lstranskyTGM/uWeatherNG/Hardware/Anemometer/Anemometer_Top.stl

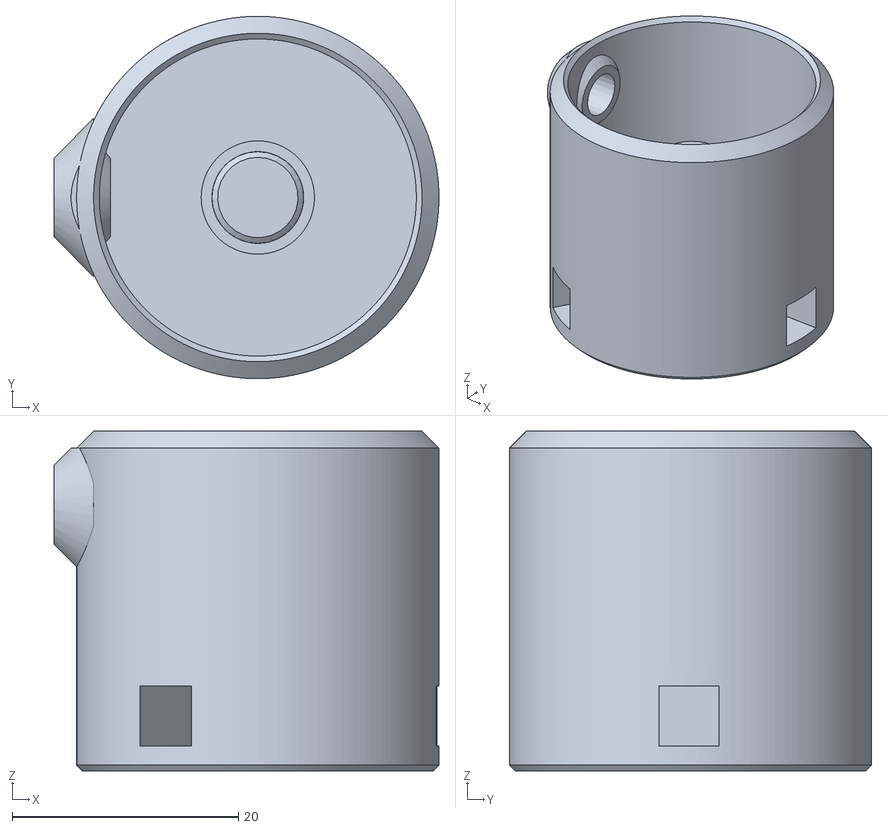
[picture p25: CAD file, 2024-08-01]
Hardware/Anemometer/Anemometer_Top.stl
34.0 x 32.0 x 30.0
