lstranskyTGM/uWeatherNG/Hardware/Connectors/Plug_Joint_ExternalThread.stl

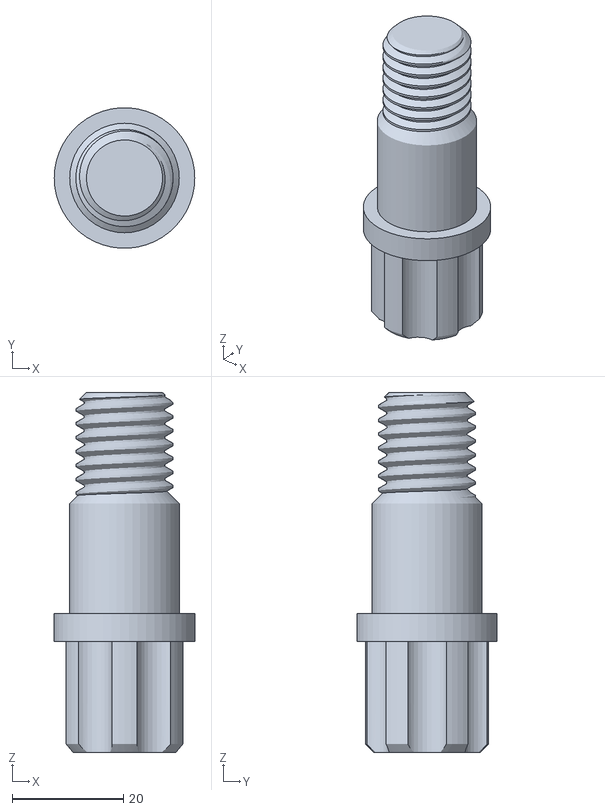
[picture p26: CAD file, 2024-08-01]
Hardware/Connectors/Plug_Joint_ExternalThread.stl
25.3 x 25.3 x 64.8
