lstranskyTGM/uWeatherNG/Hardware/Vane/Vane_Fin.stl

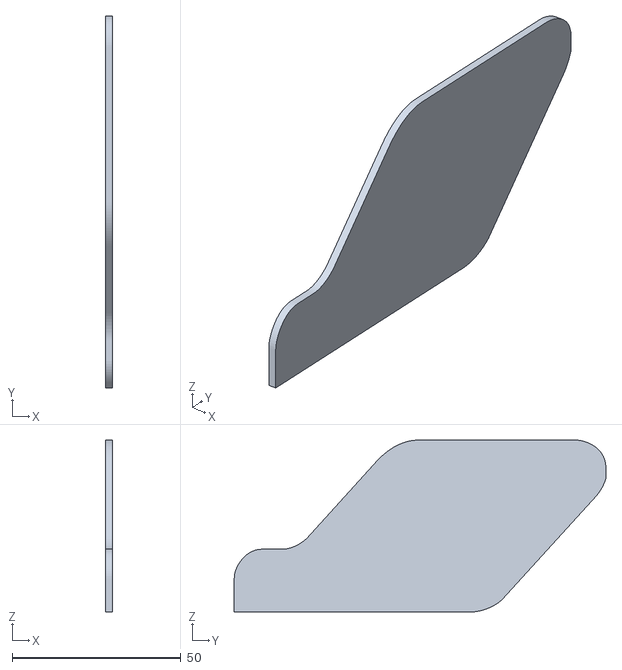
[picture p27: CAD file, 2024-08-01]
Hardware/Vane/Vane_Fin.stl
2.00 x 110.2 x 51.0
