lstranskyTGM/uWeatherNG/Hardware/Anemometer/Anemometer_Body.stl

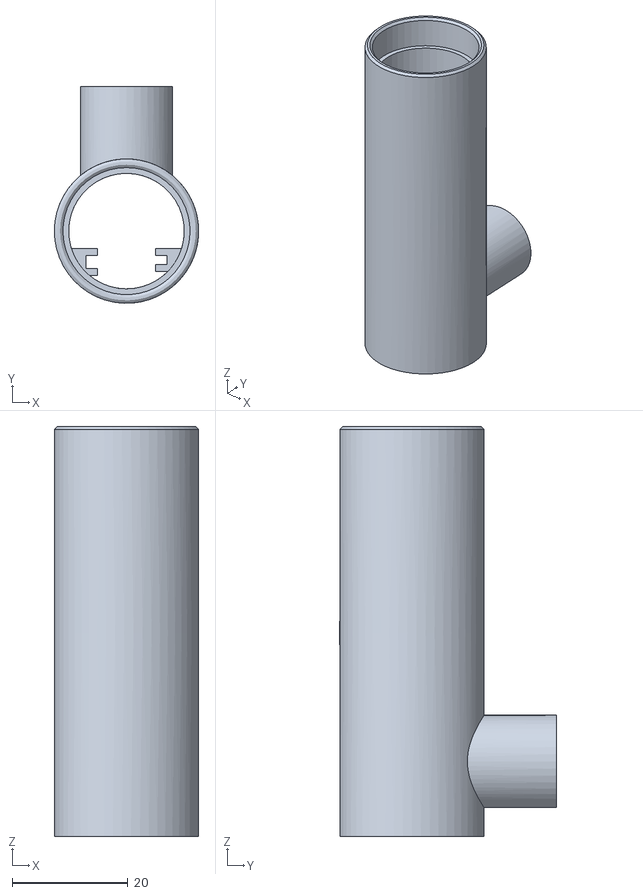
[picture p28: CAD file, 2024-08-01]
Hardware/Anemometer/Anemometer_Body.stl
25.0 x 37.5 x 71.0
