lstranskyTGM/uWeatherNG/Hardware/Connectors/Joint_InternalThread_ExternalThread.stl

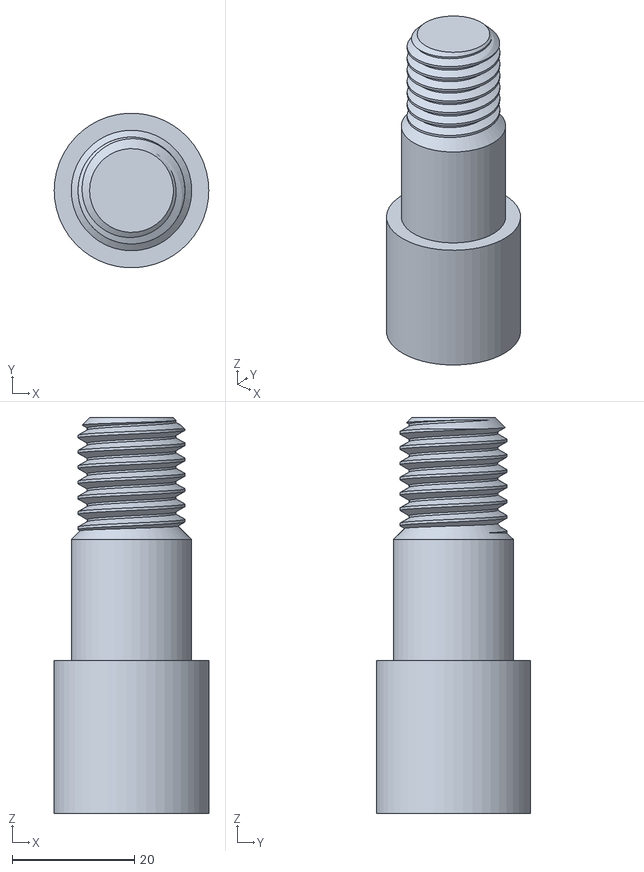
[picture p29: CAD file, 2024-08-01]
Hardware/Connectors/Joint_InternalThread_ExternalThread.stl
25.3 x 25.3 x 64.8
