lstranskyTGM/uWeatherNG/Hardware/Vane/Vane_Fin_Mount.stl

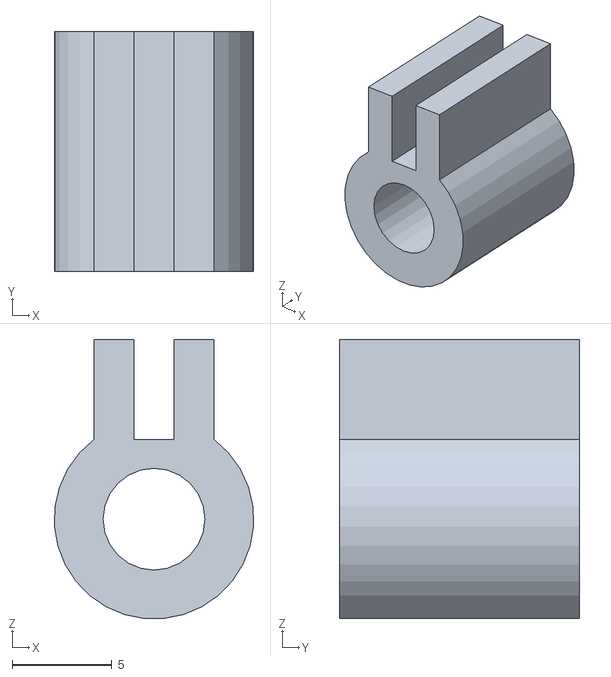
[picture p30: CAD file, 2024-08-01]
Hardware/Vane/Vane_Fin_Mount.stl
9.97 x 12.0 x 14.0
