lstranskyTGM/uWeatherNG/Hardware/Connectors/Plug_Spike.stl

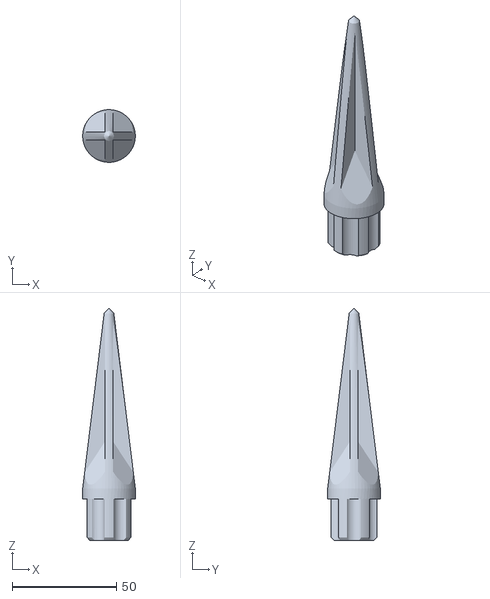
[picture p31: CAD file, 2024-08-01]
Hardware/Connectors/Plug_Spike.stl
25.3 x 25.3 x 111.4
