lstranskyTGM/uWeatherNG/Hardware/Vane/Vane_Top.stl

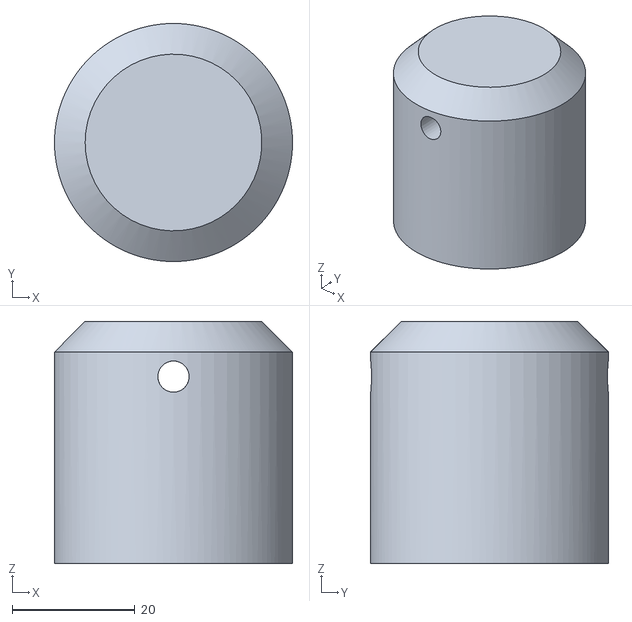
[picture p32: CAD file, 2024-08-01]
Hardware/Vane/Vane_Top.stl
38.8 x 38.8 x 39.5
