lstranskyTGM/uWeatherNG/Hardware/Connectors/Joint.stl

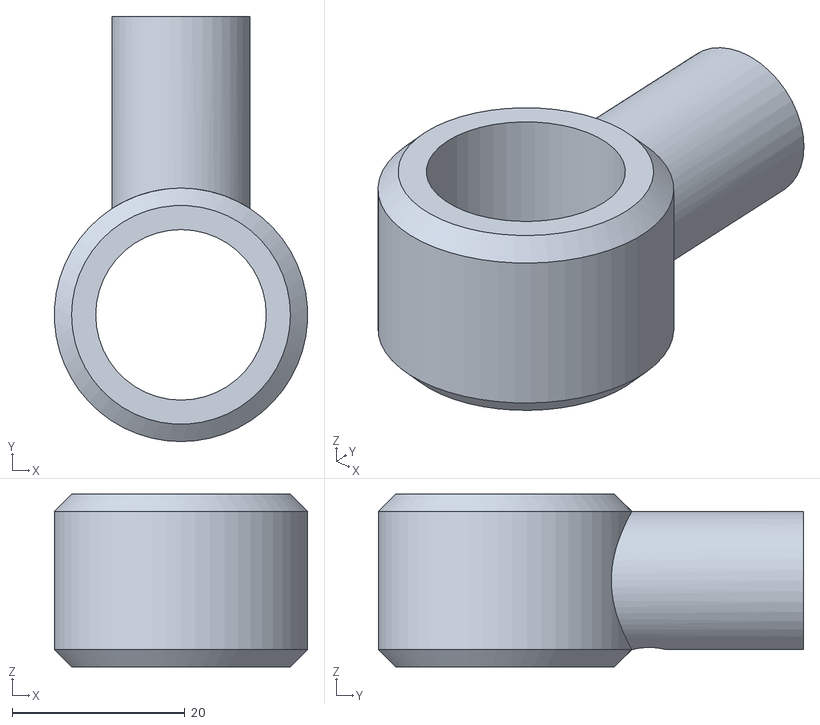
[picture p33: CAD file, 2024-08-01]
Hardware/Connectors/Joint.stl
29.3 x 49.1 x 20.0
