lstranskyTGM/uWeatherNG/Hardware/Vane/Vane_Bottom.stl

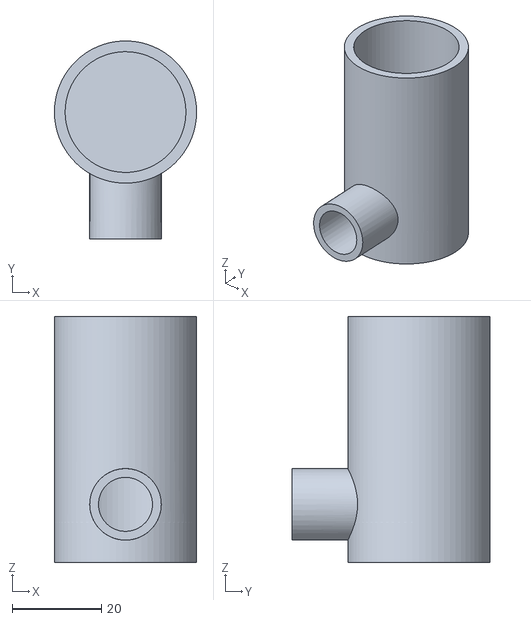
[picture p34: CAD file, 2024-08-01]
Hardware/Vane/Vane_Bottom.stl
31.8 x 44.3 x 55.0
